Howard-Z/nerf-pi/CAD_files/SG90 - Micro Servo 9g - Tower Pro.3.SLDPRT

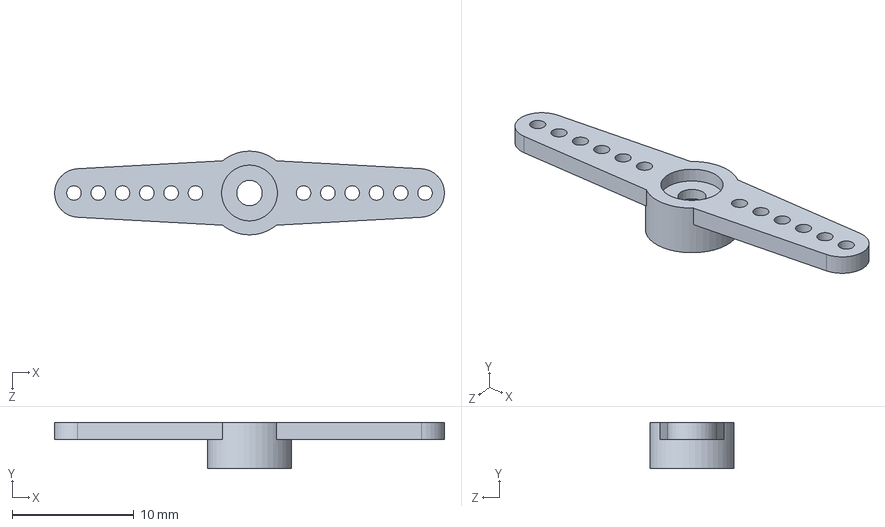
[picture p16: CAD file, 2025-06-14]
CAD_files/SG90 - Micro Servo 9g - Tower Pro.3.SLDPRT
32.1 x 3.80 x 6.90 mm
