Howard-Z/nerf-pi/CAD_files/lidGear.SLDPRT

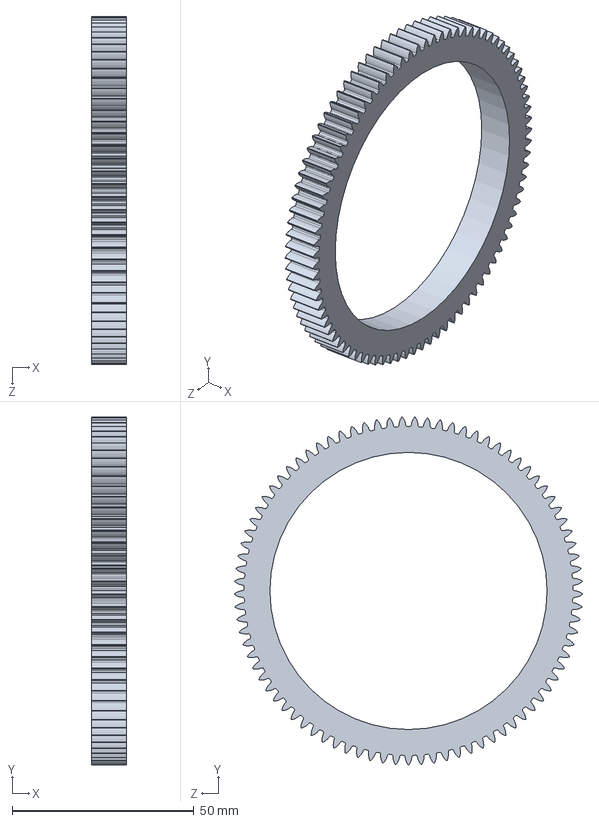
[picture p17: CAD file, 2025-06-14]
CAD_files/lidGear.SLDPRT
9.50 x 95.7 x 95.7 mm
