Howard-Z/nerf-pi/CAD_files/Stepper motor 28BYJ-48 5V.SLDPRT

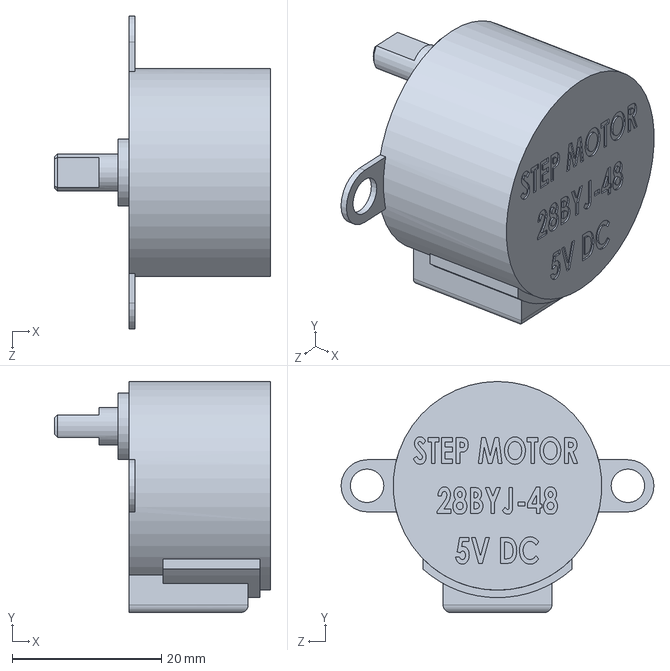
[picture p18: CAD file, 2025-06-14]
CAD_files/Stepper motor 28BYJ-48 5V.SLDPRT
29.0 x 31.0 x 42.0 mm
