Howard-Z/nerf-pi/CAD_files/SG90 - Micro Servo 9g - Tower Pro.2.SLDPRT

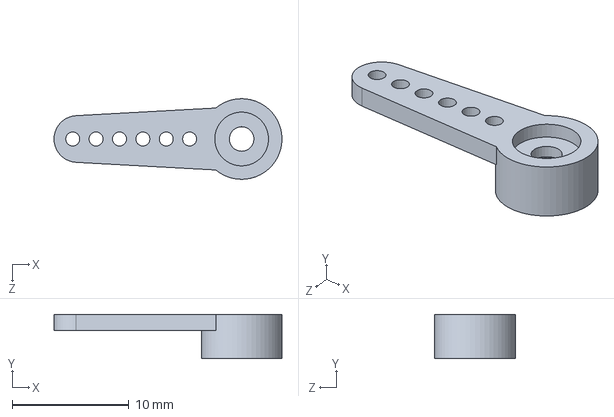
[picture p19: CAD file, 2025-06-14]
CAD_files/SG90 - Micro Servo 9g - Tower Pro.2.SLDPRT
19.5 x 3.80 x 6.90 mm
