Howard-Z/nerf-pi/pose_landmarker.py

import cv2
import mediapipe as mp
from mediapipe.tasks import python
from mediapipe.tasks.python import vision
from mediapipe.tasks.python.vision.core.vision_task_running_mode import VisionTaskRunningMode

import threading
from collections import defaultdict
from constants import MODEL_PATH, IMAGE_WIDTH, IMAGE_HEIGHT

shared_data = defaultdict(lambda: None)
data_lock = threading.Lock()

# Callback to handle results
def print_landmarks(result, output_image, timestamp_ms):
    if not result.pose_landmarks:
        print(f"[{timestamp_ms} ms] No pose detected.")
        return


    print(f"[{timestamp_ms} ms] Detected {len(result.pose_landmarks)} pose(s).")

    # landmark = result.pose_landmarks[0][17]
    # pixel_x = int(landmark.x * IMAGE_WIDTH)
    # pixel_y = int(landmark.y * IMAGE_HEIGHT)
    # print(f"Landmark 17: x={pixel_x}, y={pixel_y}, z={landmark.z:.4f}, visibility={landmark.visibility:.4f}")

    for i, landmark in enumerate(result.pose_landmarks[0]):
        pixel_x = int(landmark.x * IMAGE_WIDTH)
        pixel_y = int(landmark.y * IMAGE_HEIGHT)
        print(f"Landmark {i}: x={pixel_x}, y={pixel_y}, z={landmark.z:.4f}, visibility={landmark.visibility:.4f}")

def make_callback(cam_number):
    def callback(result, output_image, timestamp_ms):
        pose_list = []
        if result.pose_landmarks:
            for lm in result.pose_landmarks[0]:
                pose_list.append((lm.x * IMAGE_WIDTH, lm.y * IMAGE_HEIGHT))
        with data_lock:
            shared_data[cam_number] = [timestamp_ms, pose_list]

    return callback


def initialize_landmarker(cam_number: int=0, show_window: bool=False, shutdown_event: threading.Event = None):
    # Set up landmarker options
    base_options = python.BaseOptions(model_asset_path=MODEL_PATH)
    options = vision.PoseLandmarkerOptions(
        base_options=base_options,
        output_segmentation_masks=False,
        running_mode=VisionTaskRunningMode.LIVE_STREAM,
        num_poses=1,
        result_callback=make_callback(cam_number)
    )

    # Create the landmarker
    pose_landmarker = vision.PoseLandmarker.create_from_options(options)

    # Start webcam capture
    cap = cv2.VideoCapture(cam_number)


    try:
        while cap.isOpened() and (shutdown_event is None or not shutdown_event.is_set()):
            success, frame = cap.read()
            if not success:
                print("Ignoring empty frame.")
                continue

            # Convert to RGB
            frame_rgb = cv2.cvtColor(frame, cv2.COLOR_BGR2RGB)
            mp_image = mp.Image(image_format=mp.ImageFormat.SRGB, data=frame_rgb)

            # Use current time for timestamp
            timestamp = int(cap.get(cv2.CAP_PROP_POS_MSEC))
            pose_landmarker.detect_async(mp_image, timestamp)

            # Display frame
            if show_window:
                cv2.imshow("Pose Landmarker", frame)
                if cv2.waitKey(5) & 0xFF == 27:
                    break
    finally:
        cap.release()
        cv2.destroyAllWindows()
